machadoleonardo94/Myoelectric-Prosthetics/Codes/StepperDriver-master/examples/ClockStepper/ClockStepper.ino

/*
 * Clock Microstepping demo
 *
 * Moves the stepper motor like the seconds hand of a watch.
 *
 * Copyright (C)2015-2017 Laurentiu Badea
 *
 * This file may be redistributed under the terms of the MIT license.
 * A copy of this license has been included with this distribution in the file LICENSE.
 */
#include <Arduino.h>

// Motor steps per revolution. Most steppers are 200 steps or 1.8 degrees/step
#define MOTOR_STEPS 200

// Microstepping mode. If you hardwired it to save pins, set to the same value here.
#define MICROSTEPS 1

#define DIR 8
#define STEP 9
#define ENABLE 13 // optional (just delete ENABLE from everywhere if not used)

/*
 * Choose one of the sections below that match your board
 */

//#include "DRV8834.h"
//#define M0 10
//#define M1 11
//DRV8834 stepper(MOTOR_STEPS, DIR, STEP, ENABLE, M0, M1);

 #include "A4988.h"
 #define MS1 10
 #define MS2 11
 #define MS3 12
 A4988 stepper(MOTOR_STEPS, DIR, STEP, ENABLE, MS1, MS2, MS3);

// #include "DRV8825.h"
// #define MODE0 10
// #define MODE1 11
// #define MODE2 12
// DRV8825 stepper(MOTOR_STEPS, DIR, STEP, ENABLE, MODE0, MODE1, MODE2);

// #include "DRV8880.h"
// #define M0 10
// #define M1 11
// #define TRQ0 6
// #define TRQ1 7
// DRV8880 stepper(MOTOR_STEPS, DIR, STEP, ENABLE, M0, M1, TRQ0, TRQ1);

// #include "BasicStepperDriver.h" // generic
// BasicStepperDriver stepper(DIR, STEP);

void setup() {
    /*
     * Set target motor RPM=1
     */
    stepper.begin(100, MICROSTEPS);
    stepper.enable();
}

void loop() {
    /*
     * The easy way is just tell the motor to rotate 360 degrees at 1rpm
     */
    stepper.rotate(360);
}
